ChancenJ/TripleKey/README.assets/image-20240628224732417.png

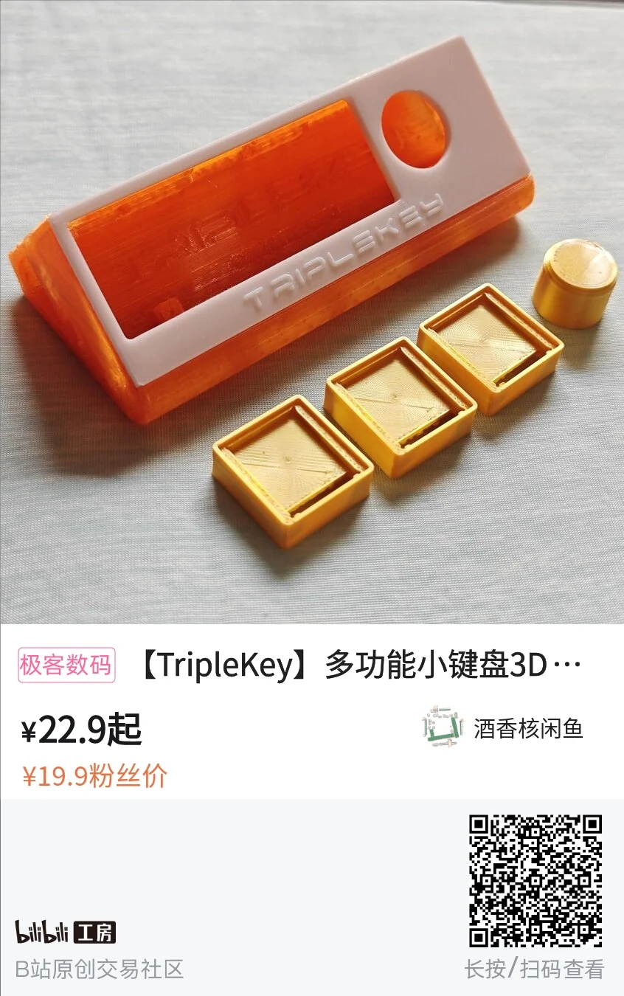
README.assets/image-20240628224732417.png
