ChancenJ/TripleKey/README.assets/IMG_20240522_190503.jpg

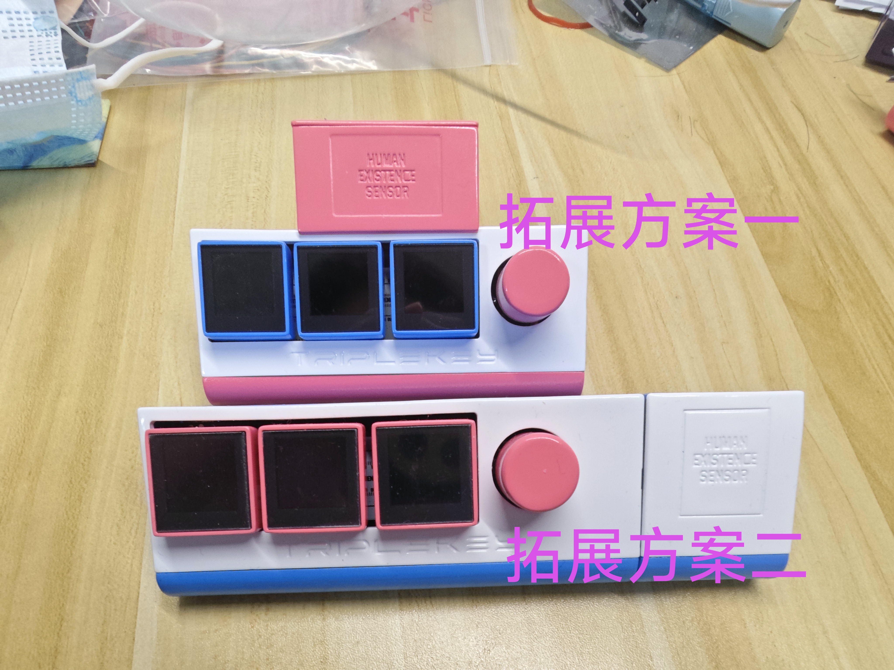
README.assets/IMG_20240522_190503.jpg
