ChancenJ/TripleKey/README.assets/IMG_20240522_190955.jpg

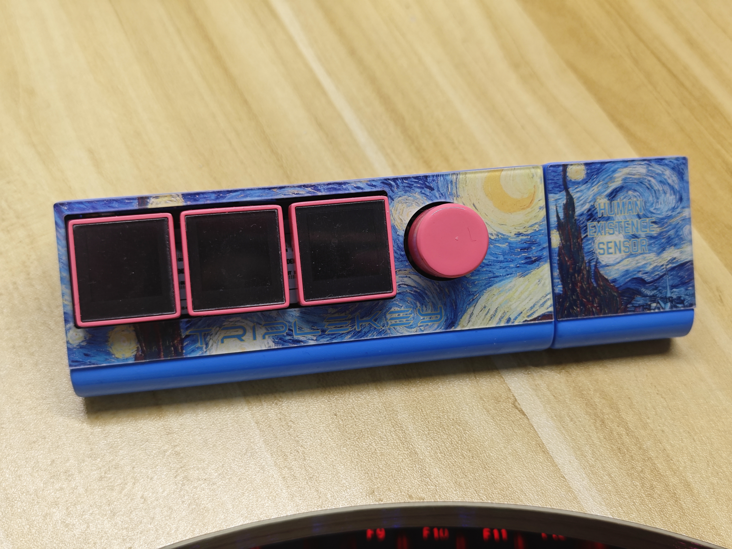
README.assets/IMG_20240522_190955.jpg
