ChancenJ/TripleKey/Software/data/photo/Example1.png

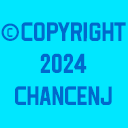
Software/data/photo/Example1.png
