ChancenJ/TripleKey/Software/data/photo/Example2.png

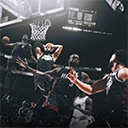
Software/data/photo/Example2.png
