ChancenJ/TripleKey/Software/data/photo/Example3.jpg

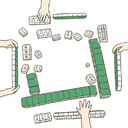
Software/data/photo/Example3.jpg
