ChancenJ/TripleKey/Software/data/PLE.png

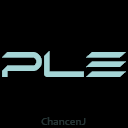
Software/data/PLE.png
