ChancenJ/TripleKey/Software/data/TRI.png

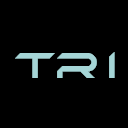
Software/data/TRI.png
