ChancenJ/TripleKey/Software/src/pages/countdown/img.h

#define img_width 48
#define img_height 48
static unsigned char img_bits[] = {
   0x00, 0x00, 0x00, 0x00, 0x00, 0x00, 0x00, 0x00, 0x00, 0x00, 0x00, 0x00,
   0x00, 0x00, 0x00, 0x00, 0x00, 0x00, 0xf0, 0xff, 0xff, 0xff, 0xff, 0x1f,
   0xf0, 0xff, 0xff, 0xff, 0xff, 0x1f, 0xf0, 0xff, 0xff, 0xff, 0xff, 0x1f,
   0xc0, 0xff, 0xff, 0xff, 0xff, 0x07, 0x00, 0x0e, 0x00, 0x00, 0xe0, 0x00,
   0x00, 0x0e, 0x00, 0x00, 0xe0, 0x00, 0x00, 0x0e, 0x00, 0x00, 0xe0, 0x00,
   0x00, 0x0e, 0x00, 0x00, 0xe0, 0x00, 0x00, 0x0e, 0x00, 0x00, 0xe0, 0x00,
   0x00, 0x0e, 0x00, 0x00, 0xe0, 0x00, 0x00, 0x0e, 0xff, 0xff, 0xf3, 0x00,
   0x00, 0x9e, 0xff, 0xff, 0xf3, 0x00, 0x00, 0x1e, 0xff, 0xff, 0x73, 0x00,
   0x00, 0x3c, 0xff, 0xff, 0x79, 0x00, 0x00, 0x3c, 0xfe, 0xff, 0x3c, 0x00,
   0x00, 0x78, 0xf8, 0x3f, 0x3c, 0x00, 0x00, 0xf0, 0xf0, 0x1f, 0x1f, 0x00,
   0x00, 0xe0, 0xc3, 0x87, 0x0f, 0x00, 0x00, 0xc0, 0x8f, 0xc3, 0x07, 0x00,
   0x00, 0x80, 0x0f, 0xe1, 0x03, 0x00, 0x00, 0x00, 0x1f, 0xf0, 0x00, 0x00,
   0x00, 0x00, 0x1f, 0xf0, 0x01, 0x00, 0x00, 0x80, 0x0f, 0xe1, 0x03, 0x00,
   0x00, 0xc0, 0x87, 0xe1, 0x07, 0x00, 0x00, 0xf0, 0xc1, 0x83, 0x0f, 0x00,
   0x00, 0xf0, 0xe0, 0x0f, 0x1f, 0x00, 0x00, 0x78, 0xf8, 0x3f, 0x3c, 0x00,
   0x00, 0x3c, 0xfc, 0x7f, 0x7c, 0x00, 0x00, 0x3c, 0xfe, 0xff, 0x78, 0x00,
   0x00, 0x1e, 0xff, 0xff, 0x71, 0x00, 0x00, 0x1e, 0xff, 0xff, 0xf1, 0x00,
   0x00, 0x8e, 0xff, 0xff, 0xf3, 0x00, 0x00, 0x8e, 0xff, 0xff, 0xe3, 0x00,
   0x00, 0xce, 0xff, 0xff, 0xe3, 0x00, 0x00, 0xce, 0xff, 0xff, 0xe3, 0x00,
   0x00, 0xce, 0xff, 0xff, 0xe7, 0x00, 0x00, 0xce, 0xff, 0xff, 0xe7, 0x00,
   0x00, 0xce, 0xff, 0xff, 0xe7, 0x00, 0xe0, 0xff, 0xff, 0xff, 0xff, 0x07,
   0xf0, 0xff, 0xff, 0xff, 0xff, 0x1f, 0xf0, 0xff, 0xff, 0xff, 0xff, 0x1f,
   0xf0, 0xff, 0xff, 0xff, 0xff, 0x1f, 0x00, 0x00, 0x00, 0x00, 0x00, 0x00,
   0x00, 0x00, 0x00, 0x00, 0x00, 0x00, 0x00, 0x00, 0x00, 0x00, 0x00, 0x00 };
