ChancenJ/TripleKey/Software/src/pages/photo/img.h

#define img_width 48
#define img_height 48
static unsigned char img_bits[] = {
   0x00, 0x00, 0x00, 0x00, 0x00, 0x00, 0x00, 0x00, 0x00, 0x00, 0x00, 0x00,
   0x00, 0x00, 0x00, 0x00, 0x00, 0x00, 0x00, 0x00, 0x00, 0x00, 0x00, 0x00,
   0x00, 0x00, 0x00, 0x00, 0x00, 0x00, 0xf0, 0xff, 0xff, 0xff, 0xff, 0x0f,
   0xf8, 0xff, 0xff, 0xff, 0xff, 0x1f, 0xfc, 0xff, 0xff, 0xff, 0xff, 0x3f,
   0xfc, 0xff, 0xff, 0xff, 0xff, 0x3f, 0xfc, 0xff, 0xff, 0xff, 0xff, 0x3f,
   0xfc, 0xff, 0xff, 0xff, 0xff, 0x3f, 0xfc, 0xff, 0xff, 0xff, 0xff, 0x3f,
   0xfc, 0xff, 0xff, 0xff, 0xff, 0x3f, 0xfc, 0xff, 0xff, 0xff, 0xff, 0x3f,
   0xfc, 0xff, 0xff, 0xff, 0xff, 0x3f, 0xfc, 0xff, 0xff, 0xff, 0xff, 0x3f,
   0xfc, 0x0f, 0xfe, 0xff, 0xff, 0x3f, 0xfc, 0x07, 0xfc, 0xff, 0xff, 0x3f,
   0xfc, 0x07, 0xfc, 0xff, 0xff, 0x3f, 0xfc, 0x07, 0xfc, 0xff, 0xff, 0x3f,
   0xfc, 0x07, 0xfc, 0xff, 0xff, 0x3f, 0xfc, 0x07, 0xfc, 0xff, 0xff, 0x3f,
   0xfc, 0x0f, 0xfe, 0xff, 0xff, 0x3f, 0xfc, 0xff, 0xff, 0xff, 0xe1, 0x3f,
   0xfc, 0xff, 0xff, 0x7f, 0xc0, 0x3f, 0xfc, 0xff, 0xff, 0x3f, 0x00, 0x3f,
   0xfc, 0xff, 0xff, 0x1f, 0x00, 0x3e, 0xfc, 0xff, 0xff, 0x07, 0x00, 0x3c,
   0xfc, 0xff, 0xff, 0x03, 0x00, 0x3c, 0xfc, 0x0f, 0xff, 0x01, 0x00, 0x3c,
   0xfc, 0x07, 0xfc, 0x00, 0x00, 0x3c, 0xfc, 0x03, 0x38, 0x00, 0x00, 0x3c,
   0xfc, 0x00, 0x10, 0x00, 0x00, 0x3c, 0x7c, 0x00, 0x00, 0x00, 0x00, 0x3c,
   0x3c, 0x00, 0x00, 0x00, 0x00, 0x3c, 0x3c, 0x00, 0x00, 0x00, 0x00, 0x3c,
   0x3c, 0x00, 0x00, 0x00, 0x00, 0x3c, 0x3c, 0x00, 0x00, 0x00, 0x00, 0x3c,
   0x3c, 0x00, 0x00, 0x00, 0x00, 0x3c, 0xfc, 0xff, 0xff, 0xff, 0xff, 0x3f,
   0xfc, 0xff, 0xff, 0xff, 0xff, 0x3f, 0xf8, 0xff, 0xff, 0xff, 0xff, 0x1f,
   0xf0, 0xff, 0xff, 0xff, 0xff, 0x0f, 0x00, 0x00, 0x00, 0x00, 0x00, 0x00,
   0x00, 0x00, 0x00, 0x00, 0x00, 0x00, 0x00, 0x00, 0x00, 0x00, 0x00, 0x00,
   0x00, 0x00, 0x00, 0x00, 0x00, 0x00, 0x00, 0x00, 0x00, 0x00, 0x00, 0x00 };
