ChancenJ/TripleKey/Software/src/pages/settings/img.h

#define img_width 48
#define img_height 48
static unsigned char img_bits[] = {
   0x00, 0x00, 0xf0, 0x0f, 0x00, 0x00, 0x00, 0x00, 0xfe, 0x7f, 0x00, 0x00,
   0x00, 0x00, 0xfe, 0x7f, 0x00, 0x00, 0x00, 0x00, 0xfe, 0x7f, 0x00, 0x00,
   0x00, 0x00, 0xfe, 0x7f, 0x00, 0x00, 0x00, 0x00, 0xff, 0xff, 0x00, 0x00,
   0x00, 0x80, 0xff, 0xff, 0x01, 0x00, 0x40, 0xc0, 0xff, 0xff, 0x03, 0x03,
   0xe0, 0xff, 0xff, 0xff, 0xff, 0x07, 0xf0, 0xff, 0xff, 0xff, 0xff, 0x0f,
   0xf0, 0xff, 0xff, 0xff, 0xff, 0x0f, 0xf8, 0xff, 0xff, 0xff, 0xff, 0x1f,
   0xfc, 0xff, 0xff, 0xff, 0xff, 0x3f, 0xfc, 0xff, 0xff, 0xff, 0xff, 0x3f,
   0xfe, 0xff, 0x1f, 0xf8, 0xff, 0x7f, 0xfe, 0xff, 0x07, 0xe0, 0xff, 0x7f,
   0xfe, 0xff, 0x01, 0x80, 0xff, 0x7f, 0xff, 0xff, 0x00, 0x00, 0xff, 0xff,
   0xfe, 0xff, 0xc0, 0x03, 0xff, 0x7f, 0xfc, 0x7f, 0xf0, 0x0f, 0xfe, 0x3f,
   0xf8, 0x3f, 0xf8, 0x1f, 0xfc, 0x1f, 0xf8, 0x3f, 0xf8, 0x1f, 0xfc, 0x1f,
   0xf0, 0x3f, 0xfc, 0x3f, 0xfc, 0x0f, 0xf0, 0x3f, 0xfc, 0x3f, 0xfc, 0x0f,
   0xf0, 0x3f, 0xfc, 0x3f, 0xfc, 0x0f, 0xf0, 0x3f, 0xfc, 0x3f, 0xfc, 0x0f,
   0xf8, 0x3f, 0xf8, 0x1f, 0xfc, 0x1f, 0xf8, 0x3f, 0xf8, 0x1f, 0xfe, 0x1f,
   0xfc, 0x7f, 0xf0, 0x0f, 0xfe, 0x3f, 0xfe, 0xff, 0xc0, 0x03, 0xff, 0x7f,
   0xff, 0xff, 0x00, 0x00, 0xff, 0xff, 0xfe, 0xff, 0x01, 0x80, 0xff, 0x7f,
   0xfe, 0xff, 0x07, 0xe0, 0xff, 0x7f, 0xfe, 0xff, 0x1f, 0xf8, 0xff, 0x7f,
   0xfc, 0xff, 0xff, 0xff, 0xff, 0x3f, 0xfc, 0xff, 0xff, 0xff, 0xff, 0x3f,
   0xf8, 0xff, 0xff, 0xff, 0xff, 0x1f, 0xf0, 0xff, 0xff, 0xff, 0xff, 0x0f,
   0xf0, 0xff, 0xff, 0xff, 0xff, 0x0f, 0xe0, 0xff, 0xff, 0xff, 0xff, 0x07,
   0xc0, 0xc0, 0xff, 0xff, 0x03, 0x03, 0x00, 0x80, 0xff, 0xff, 0x01, 0x00,
   0x00, 0x00, 0xff, 0xff, 0x00, 0x00, 0x00, 0x00, 0xfe, 0x7f, 0x00, 0x00,
   0x00, 0x00, 0xfe, 0x7f, 0x00, 0x00, 0x00, 0x00, 0xfe, 0x7f, 0x00, 0x00,
   0x00, 0x00, 0xfe, 0x7f, 0x00, 0x00, 0x00, 0x00, 0xf0, 0x0f, 0x00, 0x00 };
