ChancenJ/TripleKey/Software/src/pages/clock/img.h

#define img_width 48
#define img_height 48
static unsigned char img_bits[] = {
   0x00, 0x00, 0x00, 0x00, 0x00, 0x00, 0x00, 0x00, 0x00, 0x00, 0x00, 0x00,
   0x00, 0x00, 0x00, 0x00, 0x00, 0x00, 0x00, 0x00, 0x00, 0x00, 0x00, 0x00,
   0x00, 0x00, 0x00, 0x00, 0x00, 0x00, 0x00, 0x00, 0xfc, 0x3f, 0x00, 0x00,
   0x00, 0x80, 0xff, 0xff, 0x00, 0x00, 0x00, 0xc0, 0xff, 0xff, 0x03, 0x00,
   0x00, 0xf0, 0x7f, 0xfe, 0x0f, 0x00, 0x00, 0xf8, 0xff, 0xff, 0x1f, 0x00,
   0x00, 0xfc, 0xff, 0xff, 0x3f, 0x00, 0x00, 0xfe, 0xff, 0xff, 0x7f, 0x00,
   0x00, 0xff, 0xff, 0xff, 0xff, 0x00, 0x00, 0xff, 0xff, 0xff, 0xff, 0x00,
   0x80, 0xff, 0xff, 0xff, 0xf9, 0x01, 0x80, 0xff, 0xff, 0xff, 0xf8, 0x01,
   0xc0, 0x7f, 0xfc, 0x7f, 0xfc, 0x03, 0xc0, 0x7f, 0xf8, 0x1f, 0xfe, 0x03,
   0xe0, 0xff, 0xf1, 0x9f, 0xff, 0x07, 0xe0, 0xff, 0xe3, 0xc7, 0xff, 0x07,
   0xe0, 0xff, 0x47, 0xe2, 0xff, 0x07, 0xe0, 0xff, 0x0f, 0xf0, 0xff, 0x07,
   0xe0, 0xff, 0x1f, 0xf8, 0xff, 0x07, 0xe0, 0xfe, 0x1f, 0xf8, 0x7f, 0x07,
   0xe0, 0xfe, 0x0f, 0xf0, 0x7f, 0x07, 0xe0, 0xff, 0x1f, 0xf8, 0xff, 0x07,
   0xe0, 0xff, 0x1f, 0xf8, 0xff, 0x07, 0xe0, 0xff, 0x7f, 0xfe, 0xff, 0x07,
   0xe0, 0xff, 0xff, 0xff, 0xff, 0x07, 0xe0, 0xff, 0xff, 0xff, 0xff, 0x07,
   0xc0, 0xff, 0xff, 0xff, 0xff, 0x03, 0xc0, 0xff, 0xff, 0xff, 0xff, 0x03,
   0xc0, 0xff, 0xff, 0xff, 0xff, 0x03, 0x80, 0xff, 0xff, 0xff, 0xff, 0x01,
   0x80, 0xff, 0xff, 0xff, 0xff, 0x00, 0x00, 0xff, 0xff, 0xff, 0xff, 0x00,
   0x00, 0xfe, 0xff, 0xff, 0x7f, 0x00, 0x00, 0xfc, 0xff, 0xff, 0x3f, 0x00,
   0x00, 0xf8, 0xff, 0xff, 0x1f, 0x00, 0x00, 0xf0, 0x7f, 0xfe, 0x0f, 0x00,
   0x00, 0xc0, 0xff, 0xff, 0x03, 0x00, 0x00, 0x80, 0xff, 0xff, 0x00, 0x00,
   0x00, 0x00, 0xfc, 0x3f, 0x00, 0x00, 0x00, 0x00, 0x00, 0x00, 0x00, 0x00,
   0x00, 0x00, 0x00, 0x00, 0x00, 0x00, 0x00, 0x00, 0x00, 0x00, 0x00, 0x00,
   0x00, 0x00, 0x00, 0x00, 0x00, 0x00, 0x00, 0x00, 0x00, 0x00, 0x00, 0x00 };
