ChancenJ/TripleKey/Software/src/app/SoftwareTimer.cpp

/*
 * The MIT License (MIT)
 *
 * Copyright (c) 2019 Ha Thach (tinyusb.org) for Adafruit Industries
 *
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
 * THE SOFTWARE IS PROVIDED "AS IS", WITHOUT WARRANTY OF ANY KIND, EXPRESS OR
 * IMPLIED, INCLUDING BUT NOT LIMITED TO THE WARRANTIES OF MERCHANTABILITY,
 * FITNESS FOR A PARTICULAR PURPOSE AND NONINFRINGEMENT. IN NO EVENT SHALL THE
 * AUTHORS OR COPYRIGHT HOLDERS BE LIABLE FOR ANY CLAIM, DAMAGES OR OTHER
 * LIABILITY, WHETHER IN AN ACTION OF CONTRACT, TORT OR OTHERWISE, ARISING FROM,
 * OUT OF OR IN CONNECTION WITH THE SOFTWARE OR THE USE OR OTHER DEALINGS IN
 * THE SOFTWARE.
 */

#include "SoftwareTimer.h"
// Test if in interrupt mode

SoftwareTimer::SoftwareTimer()
{
  _handle = NULL;
}

SoftwareTimer::~SoftwareTimer()
{
  if (_handle != NULL)
    xTimerDelete(_handle, 0);
}

void SoftwareTimer::begin(uint32_t ms, TimerCallbackFunction_t callback, void *timerID, bool repeating)
{
  _handle = xTimerCreate(NULL, ms2tick(ms), repeating, timerID, callback);
}

void SoftwareTimer::setID(void *id)
{
  vTimerSetTimerID(_handle, id);
}

void *SoftwareTimer::getID(void)
{
  return pvTimerGetTimerID(_handle);
}

bool SoftwareTimer::start(void)
{
  bool ret = true;

  {
    xTimerStart(_handle, 0);
  }
  return ret;
}

bool SoftwareTimer::stop(void)
{
  bool ret = true;

  {
    xTimerStop(_handle, 0);
  }

  return ret;
}

bool SoftwareTimer::reset(void)
{
  bool ret = true;

  {
    xTimerReset(_handle, 0);
  }

  return ret;
}

bool SoftwareTimer::setPeriod(uint32_t ms)
{
  BaseType_t active = xTimerIsTimerActive(_handle);
  bool ret = true;

  {
    xTimerChangePeriod(_handle, ms2tick(ms), 0);
  }

  // Change period of inactive timer will also start it !!
  if (!active)
    stop();

  return ret;
}
